saehuihwang/cyclic_voltammetry/data/calibration_data/calibrate_1.25mM.csv

index | 0 | time (ms) | Voltage (V) | Current (mA)
scanrate (mV/s) | 160.0
scan low (V) | -1.0
scan high (V) | 1.0
num scan | 1.0
 |  | 1818200.0 | 0.024 | 2.458
 |  | 1818395.0 | 0.044 | 2.468
 |  | 1818652.0 | 0.07 | 2.47
 |  | 1819043.0 | 0.112 | 2.464
 |  | 1819299.0 | 0.138 | 2.472
 |  | 1819495.0 | 0.158 | 2.472
 |  | 1819886.0 | 0.198 | 2.472
 |  | 1820143.0 | 0.224 | 2.476
 |  | 1820340.0 | 0.244 | 2.476
 |  | 181820597.0 | 0.27 | 2.476
 |  | 1820988.0 | 0.31 | 2.472
 |  | 1821184.0 | 0.33 | 2.478
 |  | 1821441.0 | 0.354 | 2.48
 |  | 1821637.0 | 0.374 | 2.48
 |  | 1822285.0 | 0.442 | 2.482
 |  | 1822481.0 | 0.462 | 2.484
 |  | 1822738.0 | 0.488 | 2.486
 |  | 181822935.0 | 0.508 | 2.486
 |  | 1823326.0 | 0.548 | 2.482
 |  | 1823583.0 | 0.574 | 2.488
 |  | 1823779.0 | 0.594 | 2.49
 |  | 1824036.0 | 0.622 | 2.49
 |  | 18241711824232.0 | 0.642 | 2.49
 |  | 1824428.0 | 0.662 | 2.492
 |  | 1824623.0 | 0.682 | 2.492
 |  | 1824880.0 | 0.706 | 2.494
 |  | 1825137.0 | 0.732 | 2.496
 |  | 182521825334.0 | 0.752 | 2.496
 |  | 1825725.0 | 0.792 | 2.498
 |  | 1825982.0 | 0.818 | 2.5
 |  | 1826178.0 | 0.838 | 2.502
 |  | 11826436.0 | 0.864 | 2.504
 |  | 1826827.0 | 0.904 | 2.506
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
