saehuihwang/cyclic_voltammetry/data/calibration_data/calibrate_2.5mM.csv

index | 0 | time (ms) | Voltage (V) | Current (mA)
scanrate (mV/s) | 160.0
scan low (V) | -1.0
scan high (V) | 1.0
num scan | 1.0
 |  | 1615241.0 | 0.03 | 2.454
 |  | 1615632.0 | 0.07 | 2.448
 |  | 1615889.0 | 0.098 | 2.454
 |  | 1616084.0 | 0.118 | 2.456
 |  | 1616475.0 | 0.158 | 2.456
 |  | 1616732.0 | 0.184 | 2.456
 |  | 1611616927.0 | 0.204 | 2.458
 |  | 1617319.0 | 0.244 | 2.454
 |  | 1617576.0 | 0.27 | 2.462
 |  | 1617772.0 | 0.29 | 2.462
 |  | 1618029.0 | 0.316 | 2.462
 |  | 1618420.0 | 0.354 | 2.46
 |  | 1618677.0 | 0.38 | 2.464
 |  | 1618934.0 | 0.406 | 2.466
 |  | 1619131.0 | 0.428 | 2.466
 |  | 161921619326.0 | 0.448 | 2.466
 |  | 1619719.0 | 0.488 | 2.466
 |  | 1619976.0 | 0.514 | 2.47
 |  | 1620171.0 | 0.534 | 2.472
 |  | 161620428.0 | 0.558 | 2.472
 |  | 1620819.0 | 0.602 | 2.47
 |  | 1621076.0 | 0.628 | 2.476
 |  | 1621273.0 | 0.648 | 2.478
 |  | 1621530.0 | 0.672 | 2.478
 |  | 16216641621726.0 | 0.694 | 2.478
 |  | 1622178.0 | 0.738 | 2.484
 |  | 1622375.0 | 0.758 | 2.484
 |  | 1622632.0 | 0.784 | 2.488
 |  | 1621622828.0 | 0.804 | 2.49
 |  | 1623219.0 | 0.844 | 2.492
 |  | 1623476.0 | 0.87 | 2.496
 |  | 1623672.0 | 0.89 | 2.498
 |  | 1623929.0 | 0.916 | 2.5
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
