saehuihwang/cyclic_voltammetry/data/calibration_data/calibrate_5mM.csv

index | 0 | time (ms) | Voltage (V) | Current (mA)
scanrate (mV/s) | 160.0
scan low (V) | -1.0
scan high (V) | 1.0
num scan | 1.0
 |  | 553264.0 | 0.018 | 2.41
 |  | 553331.0 | 0.026 | 2.412
 |  | 553398.0 | 0.032 | 2.41
 |  | 553465.0 | 0.04 | 2.412
 |  | 553656.0 | 0.062 | 2.414
 |  | 553722.0 | 0.07 | 2.414
 |  | 553790.0 | 0.076 | 2.414
 |  | 55553913.0 | 0.09 | 2.414
 |  | 553979.0 | 0.098 | 2.414
 |  | 554047.0 | 0.106 | 2.414
 |  | 554237.0 | 0.128 | 2.416
 |  | 554304.0 | 0.134 | 2.416
 |  | 554372.0 | 0.142 | 2.416
 |  | 554494.0 | 0.156 | 2.416
 |  | 554562.0 | 0.164 | 2.416
 |  | 554629.0 | 0.172 | 2.416
 |  | 554696554752.0 | 0.186 | 2.418
 |  | 554819.0 | 0.192 | 2.418
 |  | 554886.0 | 0.2 | 2.418
 |  | 554953.0 | 0.208 | 2.418
 |  | 555076.0 | 0.22 | 2.418
 |  | 555144.0 | 0.228 | 2.418
 |  | 555211.0 | 0.236 | 2.42
 |  | 555278.0 | 0.242 | 2.42
 |  | 555345.0 | 0.25 | 2.42
 |  | 5555469.0 | 0.264 | 2.42
 |  | 555536.0 | 0.272 | 2.42
 |  | 555603.0 | 0.28 | 2.42
 |  | 555555726.0 | 0.294 | 2.422
 |  | 555794.0 | 0.3 | 2.422
 |  | 555862.0 | 0.308 | 2.422
 |  | 555928.0 | 0.316 | 2.422
 |  | 556052.0 | 0.328 | 2.422
 |  | 556119.0 | 0.336 | 2.422
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
