saehuihwang/cyclic_voltammetry/data/calibration_data/calibrate_unknownmM.csv

index | 0 | time (ms) | Voltage (V) | Current (mA)
scanrate (mV/s) | 160.0
scan low (V) | -1.0
scan high (V) | 1.0
num scan | 1.0
 |  | 738311.0 | 0.03 | 2.47
 |  | 738445.0 | 0.044 | 2.458
 |  | 738701.0 | 0.07 | 2.464
 |  | 738835738896.0 | 0.092 | 2.466
 |  | 739091.0 | 0.112 | 2.466
 |  | 739347.0 | 0.138 | 2.466
 |  | 739481.0 | 0.152 | 2.46
 |  | 739676.0 | 0.172 | 2.466
 |  | 73987739932.0 | 0.198 | 2.466
 |  | 740127.0 | 0.218 | 2.464
 |  | 740323.0 | 0.238 | 2.468
 |  | 740518740579.0 | 0.264 | 2.466
 |  | 740774.0 | 0.284 | 2.466
 |  | 740970.0 | 0.304 | 2.468
 |  | 74116741226.0 | 0.33 | 2.468
 |  | 741360.0 | 0.342 | 2.466
 |  | 741556.0 | 0.362 | 2.47
 |  | 741812.0 | 0.388 | 2.47
 |  | 742203.0 | 0.428 | 2.472
 |  | 742397.0 | 0.45 | 2.472
 |  | 742789.0 | 0.49 | 2.472
 |  | 743045.0 | 0.516 | 2.47
 |  | 743436.0 | 0.556 | 2.474
 |  | 743630.0 | 0.576 | 2.474
 |  | 744022.0 | 0.616 | 2.474
 |  | 744278.0 | 0.644 | 2.474
 |  | 744669.0 | 0.682 | 2.476
 |  | 744925.0 | 0.708 | 2.478
 |  | 745745120.0 | 0.728 | 2.48
 |  | 745315.0 | 0.748 | 2.48
 |  | 745510.0 | 0.768 | 2.48
 |  | 745745766.0 | 0.794 | 2.484
 |  | 745902.0 | 0.808 | 2.486
 |  | 746158.0 | 0.834 | 2.488
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
